JCVillanova/ucla-ceed-rover-fall-2024/CAD/ROVER_PARTS_NEW/L298N.SLDPRT

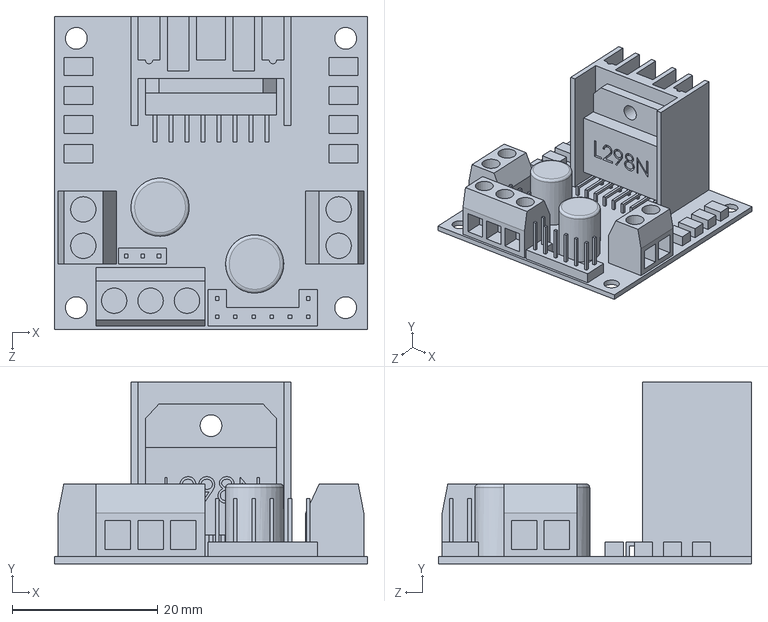
[picture p16: CAD file, 2024-10-18]
CAD/ROVER_PARTS_NEW/L298N.SLDPRT
43.0 x 25.0 x 43.0 mm
