JCVillanova/ucla-ceed-rover-fall-2024/CAD/Provided Parts/MOTOR.SLDPRT

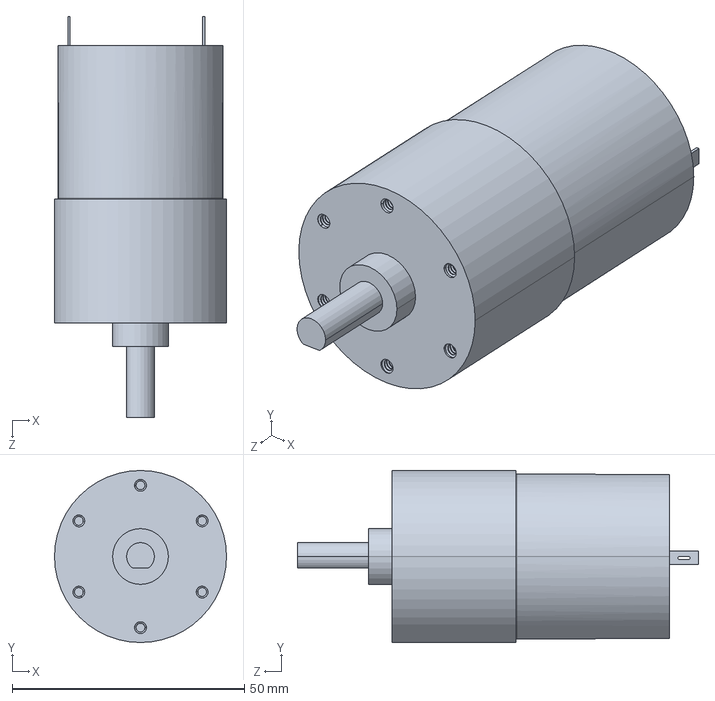
[picture p17: CAD file, 2024-10-15]
CAD/Provided Parts/MOTOR.SLDPRT
37.0 x 37.0 x 86.3 mm
