JCVillanova/ucla-ceed-rover-fall-2024/CAD/ROVER_PARTS_NEW/UltrasonicHolder_(new) (1).SLDPRT

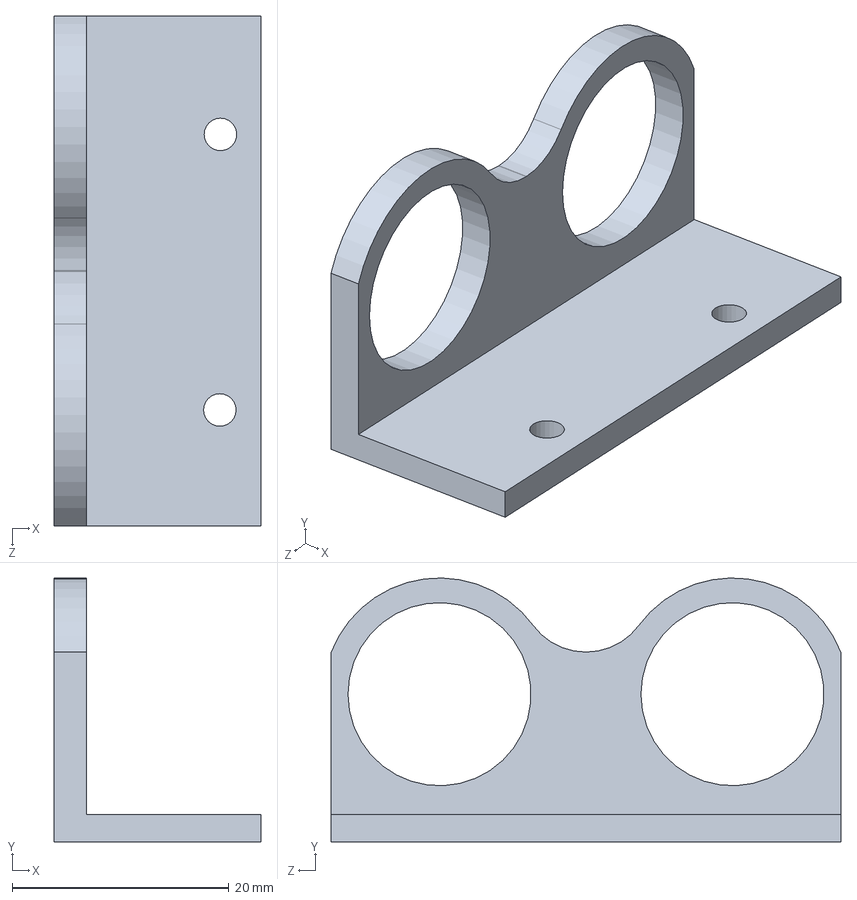
[picture p18: CAD file, 2024-10-18]
CAD/ROVER_PARTS_NEW/UltrasonicHolder_(new) (1).SLDPRT
19.1 x 24.3 x 47.0 mm
