JCVillanova/ucla-ceed-rover-fall-2024/CAD/ROVER_PARTS_NEW/ULTRASONIC SENSOR.SLDPRT

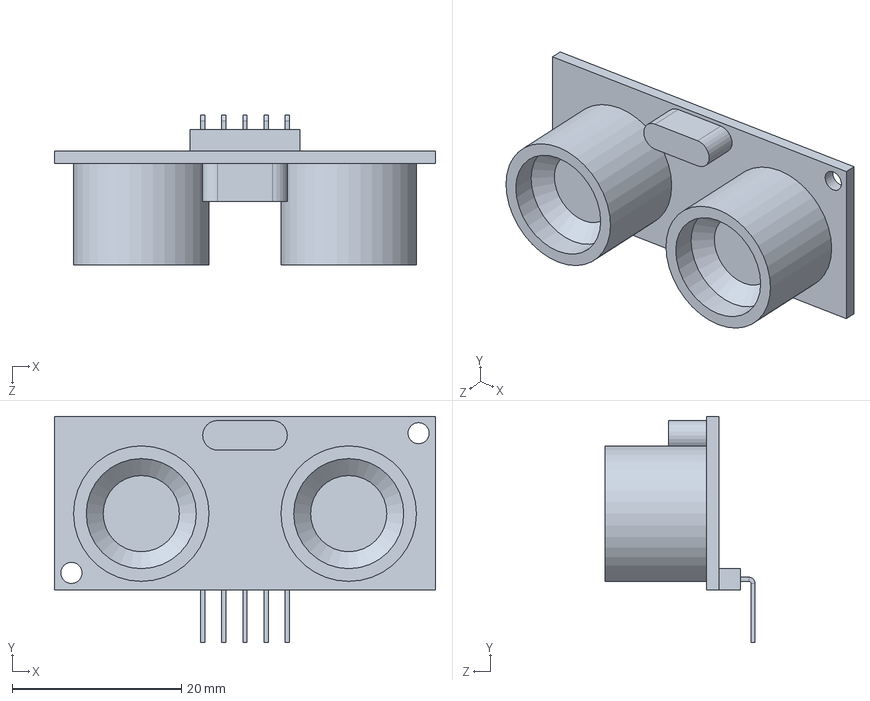
[picture p19: CAD file, 2024-10-18]
CAD/ROVER_PARTS_NEW/ULTRASONIC SENSOR.SLDPRT
45.0 x 26.8 x 17.8 mm
