JCVillanova/ucla-ceed-rover-fall-2024/CAD/Sher-ray_SensorHolder.SLDPRT

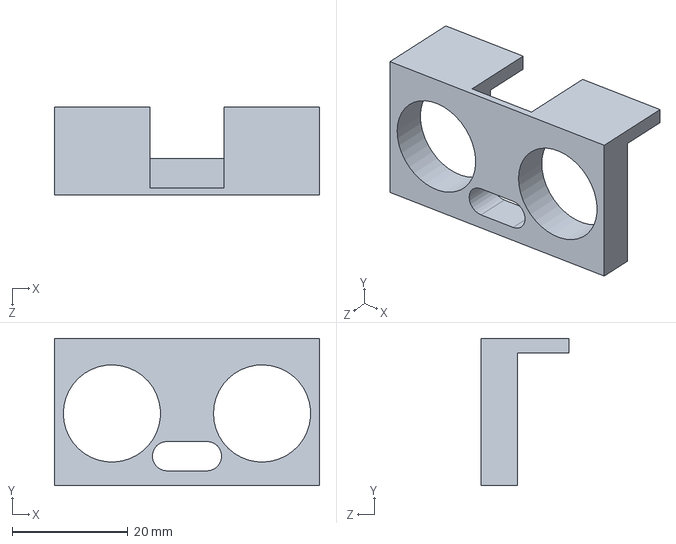
[picture p20: CAD file, 2024-10-18]
CAD/Sher-ray_SensorHolder.SLDPRT
45.7 x 25.4 x 15.2 mm
