JCVillanova/ucla-ceed-rover-fall-2024/CAD/ENGR 1 ACT 2.SLDPRT

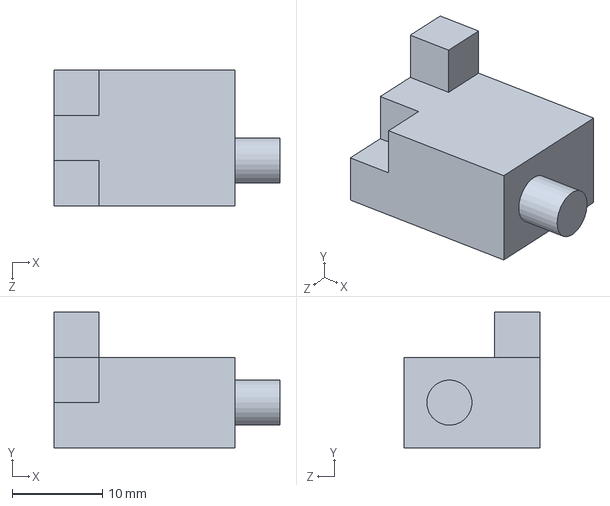
[picture p21: CAD file, 2024-10-15]
CAD/ENGR 1 ACT 2.SLDPRT
25.0 x 15.0 x 15.0 mm
