JCVillanova/ucla-ceed-rover-fall-2024/CAD/ROVER_PARTS_NEW/FinalRoverWheel.SLDPRT

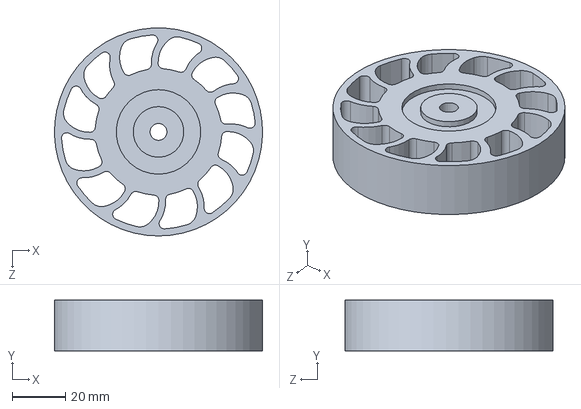
[picture p22: CAD file, 2024-10-18]
CAD/ROVER_PARTS_NEW/FinalRoverWheel.SLDPRT
78.2 x 19.1 x 78.1 mm
