JCVillanova/ucla-ceed-rover-fall-2024/CAD/ROVER_PARTS_NEW/Battery Holder- Bottom.SLDPRT

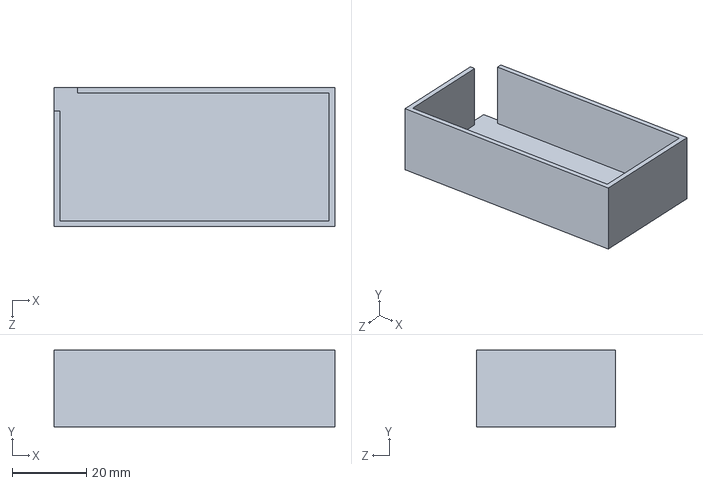
[picture p23: CAD file, 2024-10-18]
CAD/ROVER_PARTS_NEW/Battery Holder- Bottom.SLDPRT
75.6 x 20.6 x 37.5 mm
