JCVillanova/ucla-ceed-rover-fall-2024/CAD/ROVER_PARTS_NEW/STD Servomotor.SLDPRT

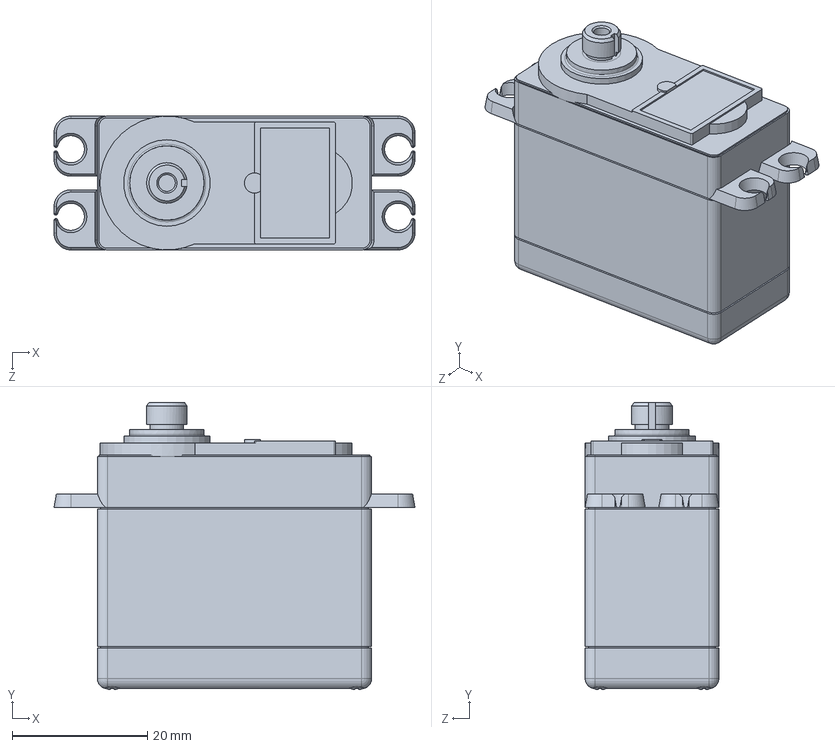
[picture p24: CAD file, 2024-10-18]
CAD/ROVER_PARTS_NEW/STD Servomotor.SLDPRT
53.4 x 42.5 x 19.8 mm
