JCVillanova/ucla-ceed-rover-fall-2024/CAD/ROVER_PARTS_NEW/UltrasonicHolder.STL

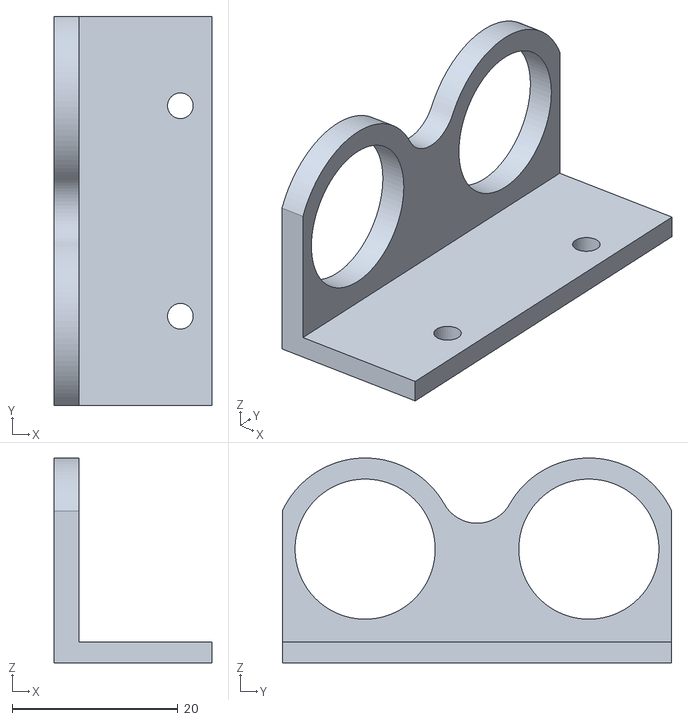
[picture p25: CAD file, 2024-10-18]
CAD/ROVER_PARTS_NEW/UltrasonicHolder.STL
19.0 x 47.0 x 24.7
