JCVillanova/ucla-ceed-rover-fall-2024/CAD/ROVER_PARTS_NEW/Wheel_example.SLDPRT

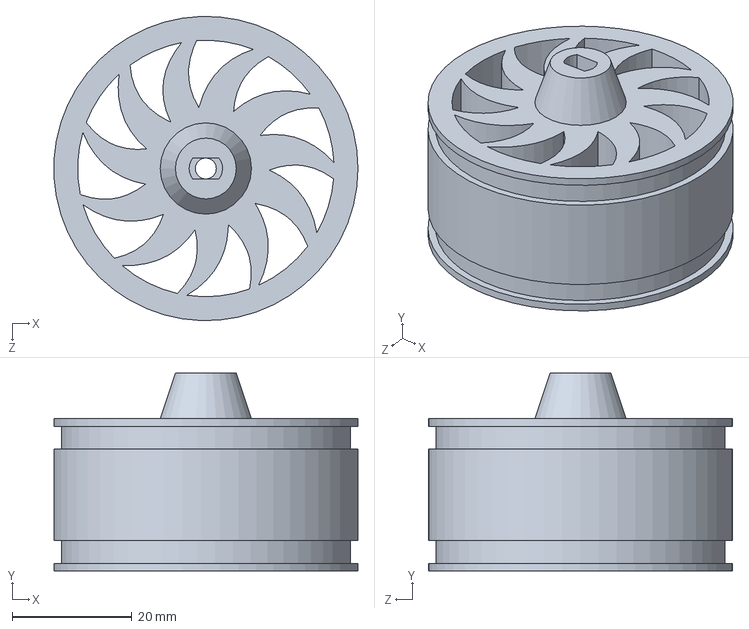
[picture p26: CAD file, 2024-10-18]
CAD/ROVER_PARTS_NEW/Wheel_example.SLDPRT
50.8 x 33.0 x 50.8 mm
