JCVillanova/ucla-ceed-rover-fall-2024/CAD/ROVER_PARTS_NEW/motor_rough.SLDPRT

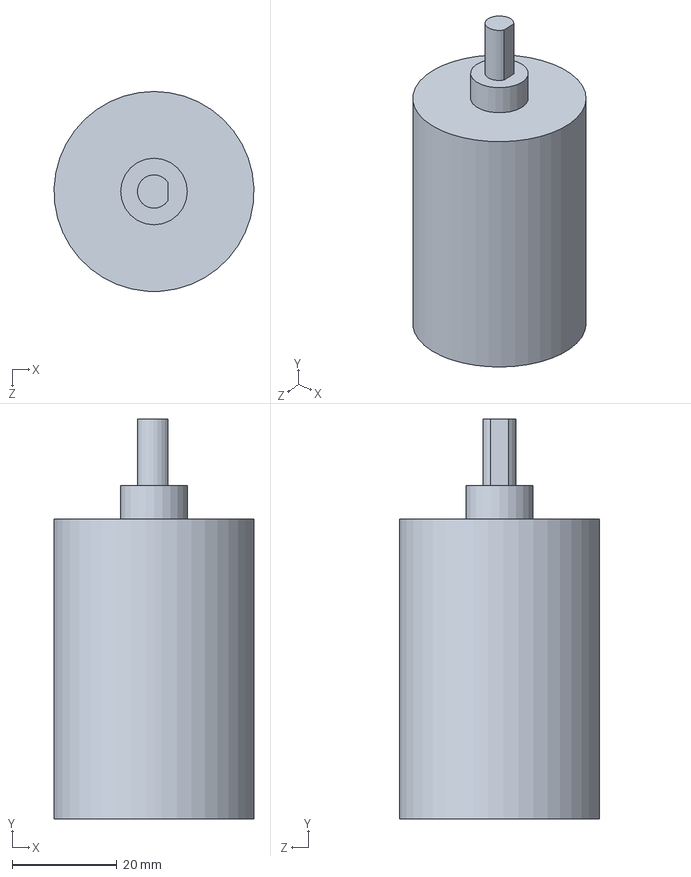
[picture p27: CAD file, 2024-10-18]
CAD/ROVER_PARTS_NEW/motor_rough.SLDPRT
38.1 x 76.2 x 38.1 mm
