JCVillanova/ucla-ceed-rover-fall-2024/CAD/ROVER_PARTS_NEW/Motor Clamp.SLDPRT

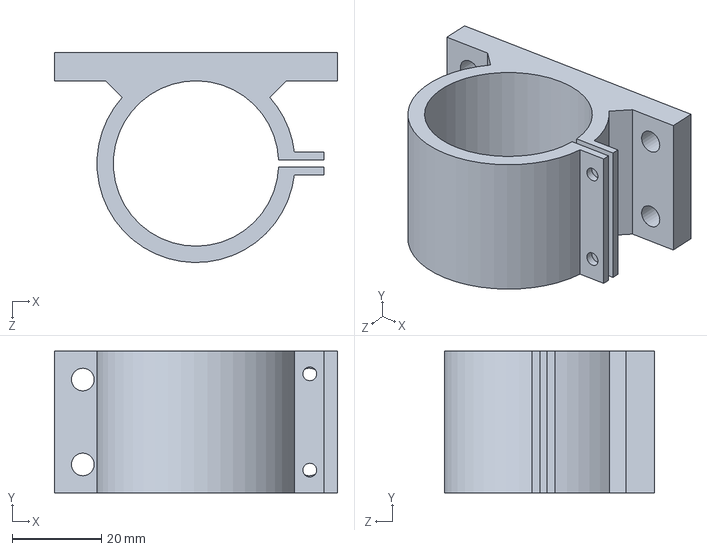
[picture p28: CAD file, 2024-10-18]
CAD/ROVER_PARTS_NEW/Motor Clamp.SLDPRT
63.5 x 31.8 x 47.1 mm
